geaz/syncBlink/img/cover2.jpg

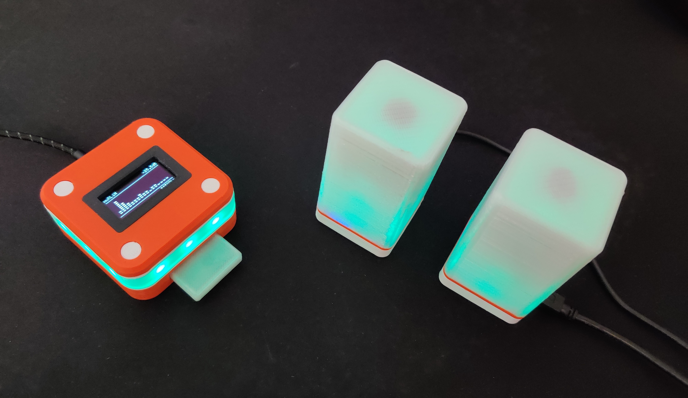
img/cover2.jpg
