geaz/syncBlink/img/hub/stripboard.jpg

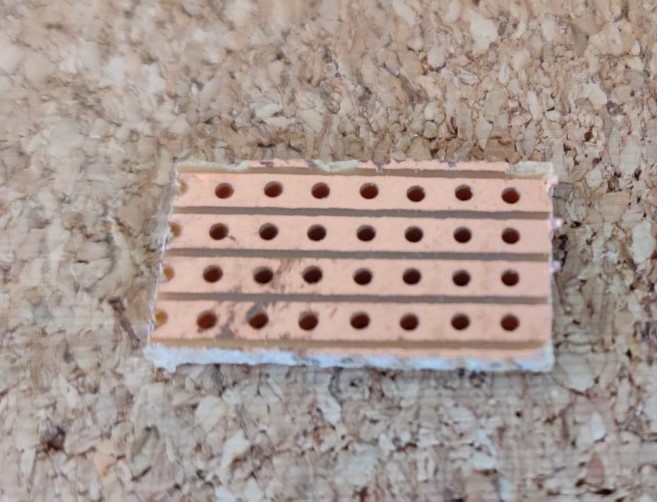
img/hub/stripboard.jpg
