geaz/syncBlink/img/mesh.png

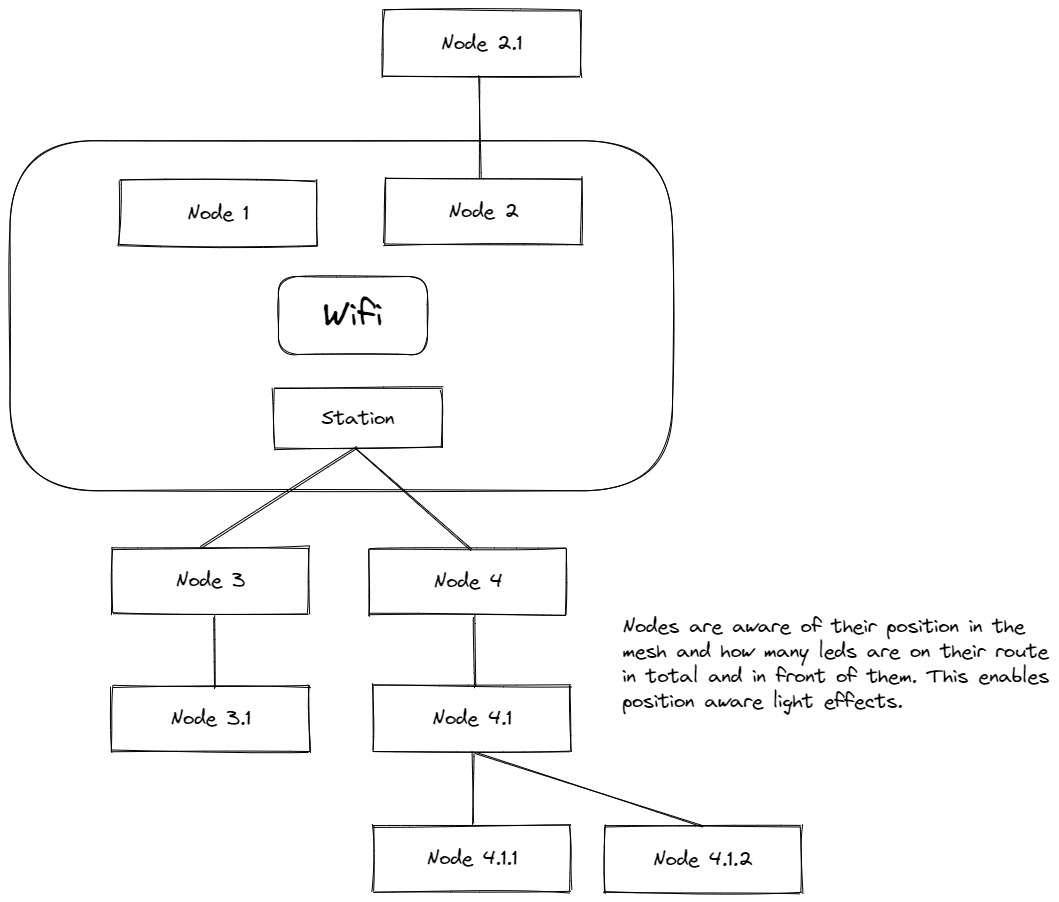
img/mesh.png
