geaz/syncBlink/stl/matrix/PixelGrid.stl

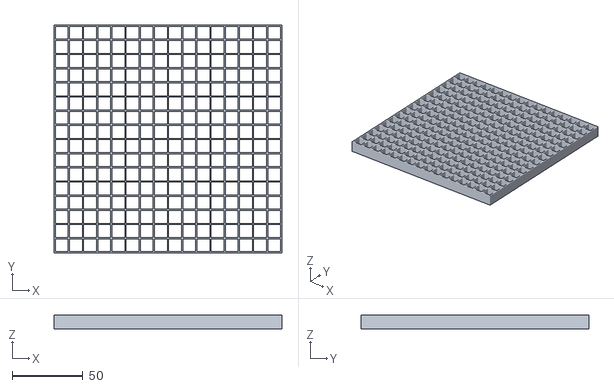
[picture p36: CAD file, 2021-04-25]
stl/matrix/PixelGrid.stl
161.0 x 161.0 x 10.0
