geaz/syncBlink/stl/hub/4x Bolt.stl

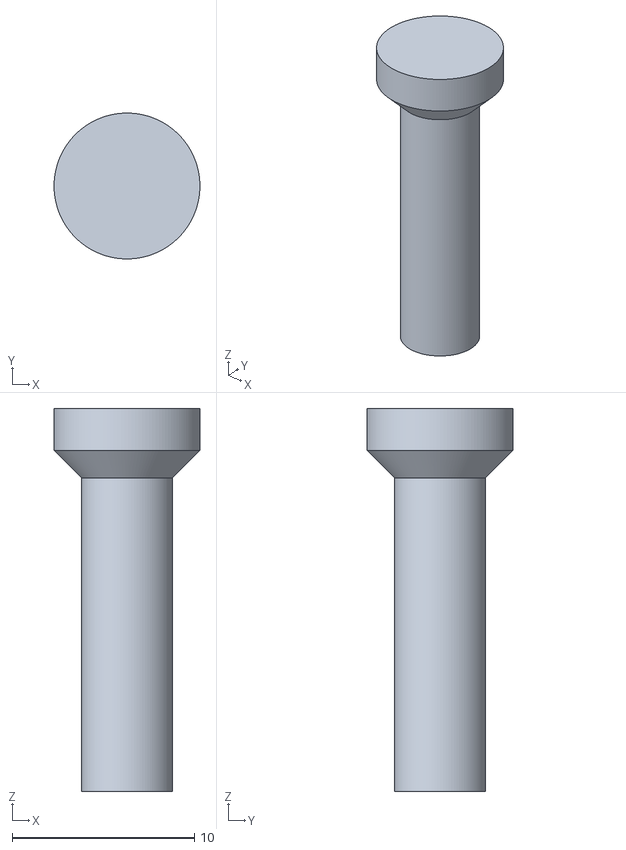
[picture p37: CAD file, 2021-04-25]
stl/hub/4x Bolt.stl
8.00 x 8.00 x 21.0
