geaz/syncBlink/src/firmware/src/modules/node_wifi_module.cpp

#include "node_wifi_module.hpp"

#include "core/message/messages/mesh_connection.hpp"
#include "core/network/get_id.hpp"

namespace SyncBlink
{
    NodeWifiModule::NodeWifiModule(Config& config, LED& led, MessageBus& messageBus, ScriptList& scriptList, MeshInfo& meshInfo)
        : _config(config), _led(led), _messageBus(messageBus), _scriptList(scriptList), _meshInfo(meshInfo),
          _mesh(_config.Values[F("wifi_ssid")], _config.Values[F("wifi_pw")]), _tcpServer(_messageBus)
    {
        _meshHandleId = _messageBus.addMsgHandler<Messages::MeshConnection>(MessageType::MeshConnection, this);
        _meshUpdateHandleId = _messageBus.addMsgHandler<Messages::MeshUpdate>(MessageType::MeshUpdate, this);
        _analyzerHandleId = _messageBus.addMsgHandler<Messages::AnalyzerUpdate>(MessageType::AnalyzerUpdate, this);
        _nodeCommandHandleId = _messageBus.addMsgHandler<Messages::NodeCommand>(MessageType::NodeCommand, this);
        _rawHandleId = _messageBus.addMsgHandler<Messages::RawBytes>(MessageType::RawBytes, this);
    }

    NodeWifiModule::~NodeWifiModule()
    {
        _messageBus.removeMsgHandler(_meshHandleId);
        _messageBus.removeMsgHandler(_meshUpdateHandleId);
        _messageBus.removeMsgHandler(_analyzerHandleId);
        _messageBus.removeMsgHandler(_nodeCommandHandleId);
        _messageBus.removeMsgHandler(_rawHandleId);
    }

    void NodeWifiModule::setup()
    {
        _mesh.connectWifi();
        if (!_mesh.tryJoinMesh())
        {
            Serial.print(F("[NODE] Not connected to mesh. Going to sleep and trying again later ...\n"));
            _led.showNow(Colors::Black);
            ESP.deepSleep(SleepSeconds * 1000000);
        }

        _tcpClient = std::make_shared<TcpClient>(_messageBus);
        _tcpClient->start(_mesh.getParentIp().toString(), 81);
        _tcpServer.start();

        Messages::MeshConnection msg;
        msg.nodeId = SyncBlink::getId();
        msg.isConnected = true;
        msg.nodeInfo = std::get<1>(_meshInfo.getLocalNodeInfo());
        msg.nodeInfo.connectedToMeshWifi = _mesh.isConnectedToMeshWifi();

        _lastReceivedPing = millis(); // init variable
        _tcpClient->writeMessage(msg.toPackage());
    }

    void NodeWifiModule::loop()
    {
        _tcpServer.loop();
        _tcpClient->loop();

        if (!_tcpClient->isConnected() || millis() - _lastReceivedPing > 10000) // The last ping was 10 seconds ago. Likely disconnected.
        {
            Serial.print(F("Going to sleep ...\n"));
            _led.showNow(Colors::Black);
            ESP.deepSleep(SleepSeconds * 1000000);
        }
    }

    void NodeWifiModule::onMsg(const Messages::MeshConnection& msg)
    {
        _tcpClient->writeMessage(msg.toPackage());
    }

    void NodeWifiModule::onMsg(const Messages::MeshUpdate& msg)
    {
        Messages::MeshUpdate updatedMsg;
        updatedMsg.meshLedCount = msg.meshLedCount;
        updatedMsg.meshNodeCount = msg.meshLedCount;
        updatedMsg.routeLedCount = msg.routeLedCount + _config.Values[F("led_count")].as<uint32_t>();
        updatedMsg.routeNodeCount = msg.routeNodeCount + 1;

        _tcpServer.broadcast(updatedMsg.toPackage());
    }

    void NodeWifiModule::onMsg(const Messages::AnalyzerUpdate& msg)
    {
        _tcpServer.broadcast(msg.toPackage());
    }

    void NodeWifiModule::onMsg(const Messages::RawBytes& msg)
    {
        if (msg.recipientId != SyncBlink::getId() || msg.recipientId == 0) _tcpServer.broadcast(msg.toPackage());
        if (msg.recipientId != SyncBlink::getId() && msg.recipientId != 0) return;        
        if(!_isReceivingScript) return;

        _activeScriptReceive.getBytecodeFile(true).write(&msg.bytes[0], msg.byteCount);
    }

    void NodeWifiModule::onMsg(const Messages::NodeCommand& msg)
    {
        if (msg.recipientId != SyncBlink::getId() || msg.recipientId == 0) _tcpServer.broadcast(msg.toPackage());
        if (msg.recipientId != SyncBlink::getId() && msg.recipientId != 0) return;

        switch (msg.commandType)
        {
        case Messages::NodeCommandType::Ping:
            // Only if the ping is not directed to the whole mesh, react with a blink
            // Otherwise it is the occasional connection check ping from the hub
            _lastReceivedPing = millis();
            if(msg.recipientId != 0) _led.blinkNow(Colors::Blue);
            break;
        case Messages::NodeCommandType::Rename:
            _config.Values[F("name")] = msg.commandInfo.stringInfo1;
            _config.save();
            break;
        case Messages::NodeCommandType::WifiChange:
            if (msg.commandInfo.flag)
            {
                _config.Values[F("wifi_ssid")] = nullptr;
                _config.Values[F("wifi_pw")] = nullptr;
            }
            else
            {
                _config.Values[F("wifi_ssid")] = msg.commandInfo.stringInfo1;
                _config.Values[F("wifi_pw")] = msg.commandInfo.stringInfo2;
            }

            _config.save();
            ESP.restart();
            break;
        case Messages::NodeCommandType::ScriptUpdate:
            _isReceivingScript = true;
            _activeScriptReceive = _scriptList.get(msg.commandInfo.stringInfo1);
            break;
        case Messages::NodeCommandType::ScriptUpdated:
            _isReceivingScript = false;
            _activeScriptReceive.closeFile();
        case Messages::NodeCommandType::ScriptLoadCmd:
            _messageBus.trigger(Messages::ScriptLoad{_activeScriptReceive.Name});
            break;
        }
    }
}
